houseofdouglas/open-capture/scanner_rig/stl/turntable_bracket.3mf

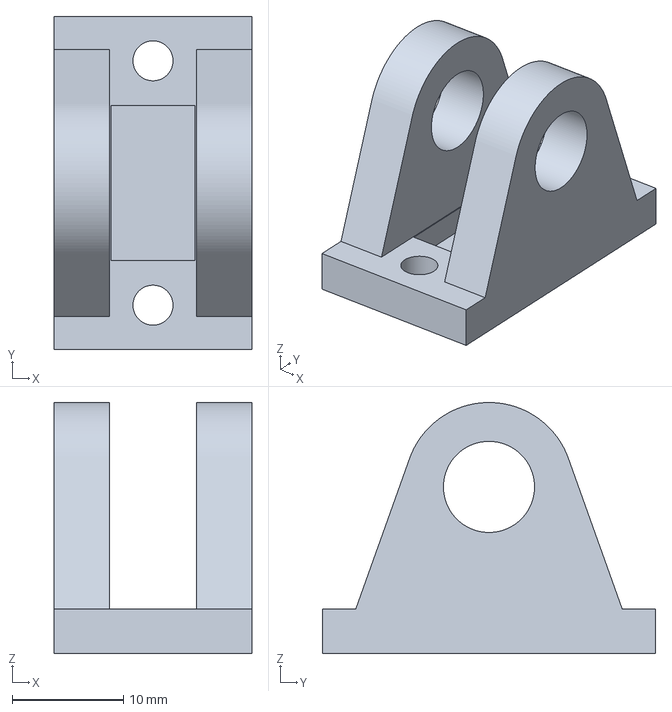
[picture p15: CAD file, 2026-07-24]
scanner_rig/stl/turntable_bracket.3mf
17.8 x 30.0 x 22.6 mm
